tfy17pmk/dbt/GUI/assets/circle.png

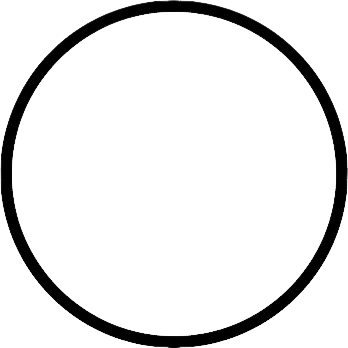
GUI/assets/circle.png
