tfy17pmk/dbt/GUI/assets/competition.png

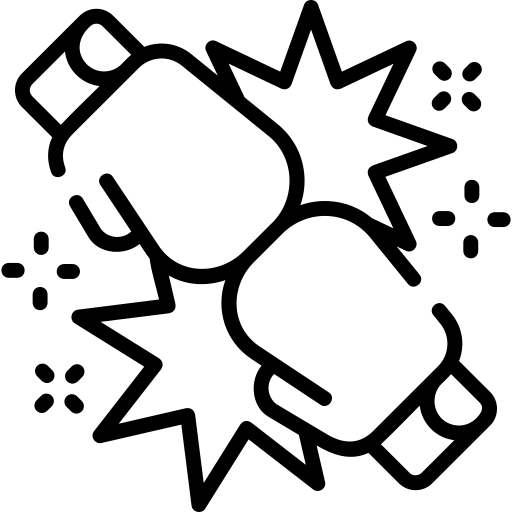
GUI/assets/competition.png
