tfy17pmk/dbt/GUI/assets/ENFlag.png

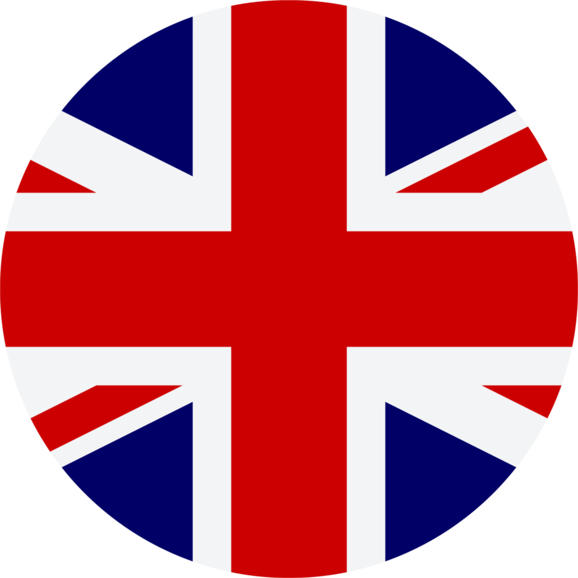
GUI/assets/ENFlag.png
