tfy17pmk/dbt/GUI/assets/heart.png

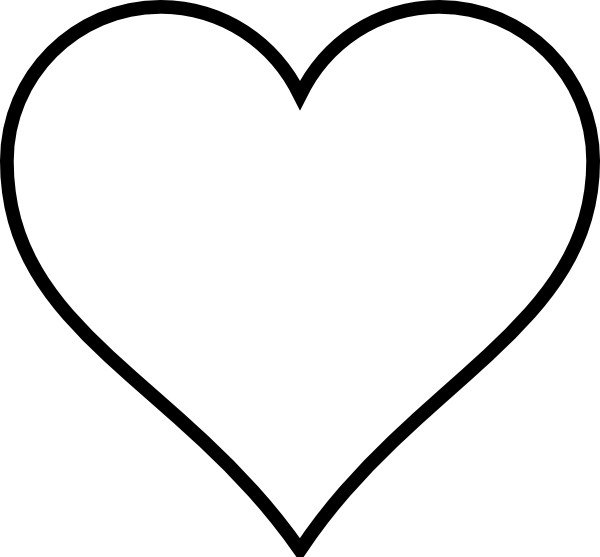
GUI/assets/heart.png
