tfy17pmk/dbt/Parts/waterLaserCutting/3mmMDF/BottomRoundBox.dxf

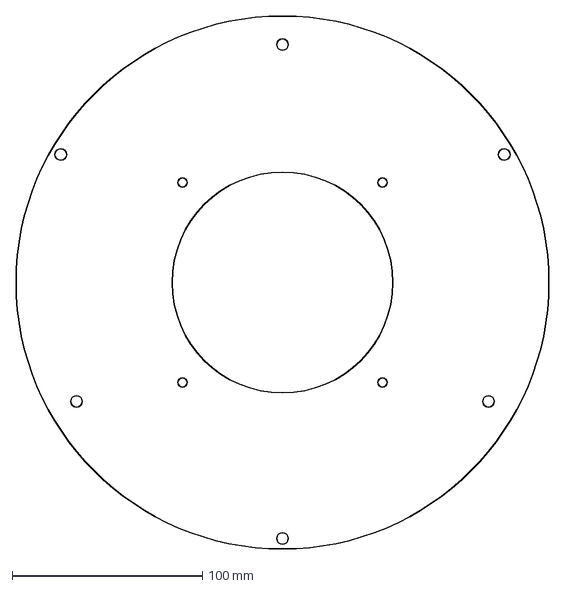
[picture p23: CAD file, 2024-12-10]
Parts/waterLaserCutting/3mmMDF/BottomRoundBox.dxf
280.0 x 280.0 mm
