tfy17pmk/dbt/Parts/waterLaserCutting/3mmMDF/CirkularBoxInsert/Bottom.dxf

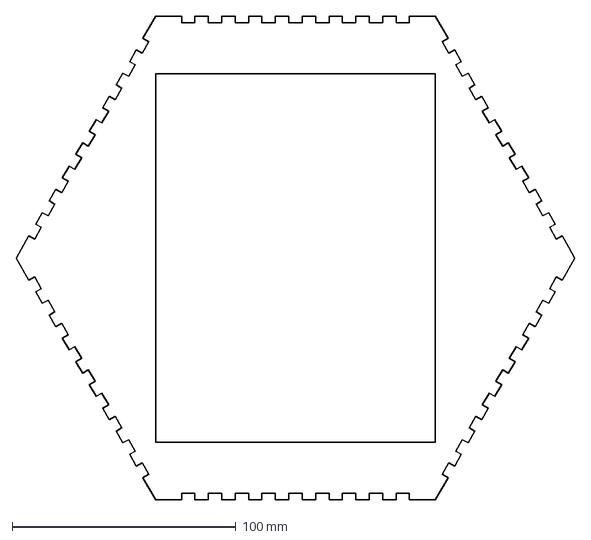
[picture p24: CAD file, 2024-12-10]
Parts/waterLaserCutting/3mmMDF/CirkularBoxInsert/Bottom.dxf
250.0 x 216.5 mm
