tfy17pmk/dbt/Parts/waterLaserCutting/metal/MonitorCover1mm.dxf

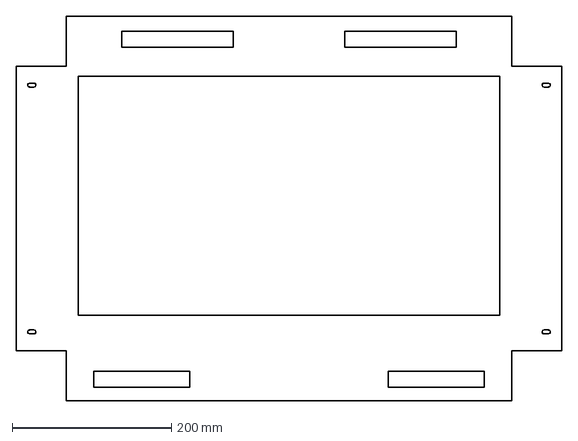
[picture p25: CAD file, 2024-12-17]
Parts/waterLaserCutting/metal/MonitorCover1mm.dxf
685.3 x 483.3 mm
