tfy17pmk/dbt/Parts/stl Files/Arm/LowerArmpartB.stl

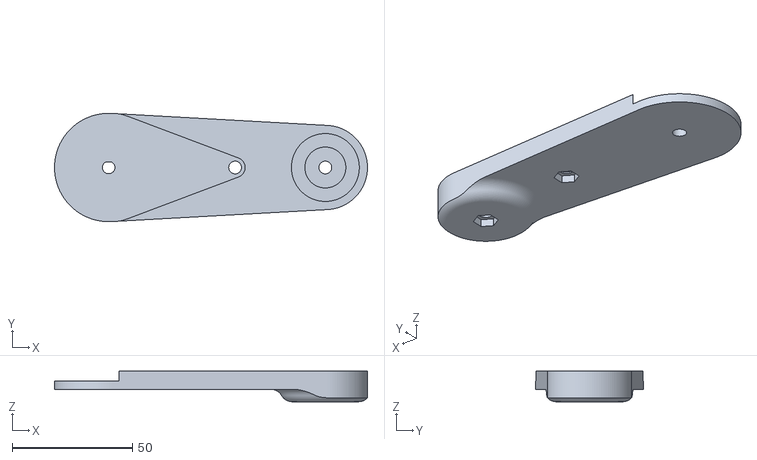
[picture p26: CAD file, 2024-12-10]
Parts/stl Files/Arm/LowerArmpartB.stl
130.0 x 45.0 x 12.7
