tfy17pmk/dbt/Parts/stl Files/Balance Plate Mounting Bracket/BottomBracket.stl

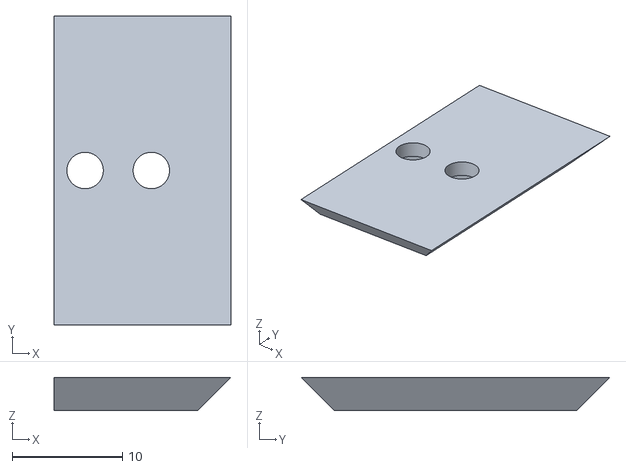
[picture p27: CAD file, 2024-12-10]
Parts/stl Files/Balance Plate Mounting Bracket/BottomBracket.stl
16.0 x 28.0 x 3.00
