tfy17pmk/dbt/Parts/stl Files/PSUcover.stl

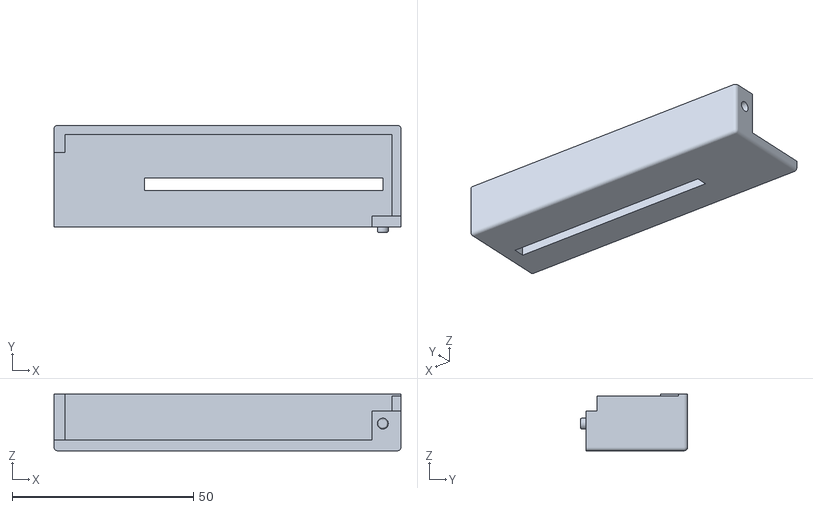
[picture p28: CAD file, 2024-12-10]
Parts/stl Files/PSUcover.stl
95.6 x 29.6 x 15.6
