tfy17pmk/dbt/Parts/waterLaserCutting/metal/SmalMetalRingWithNotch3mm.dxf

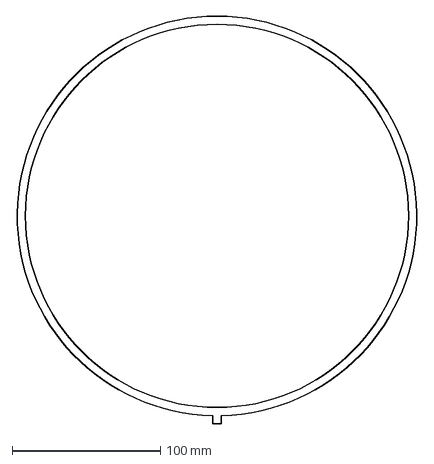
[picture p29: CAD file, 2024-12-10]
Parts/waterLaserCutting/metal/SmalMetalRingWithNotch3mm.dxf
270.6 x 274.5 mm
