tfy17pmk/dbt/Parts/stl Files/CableClip.stl

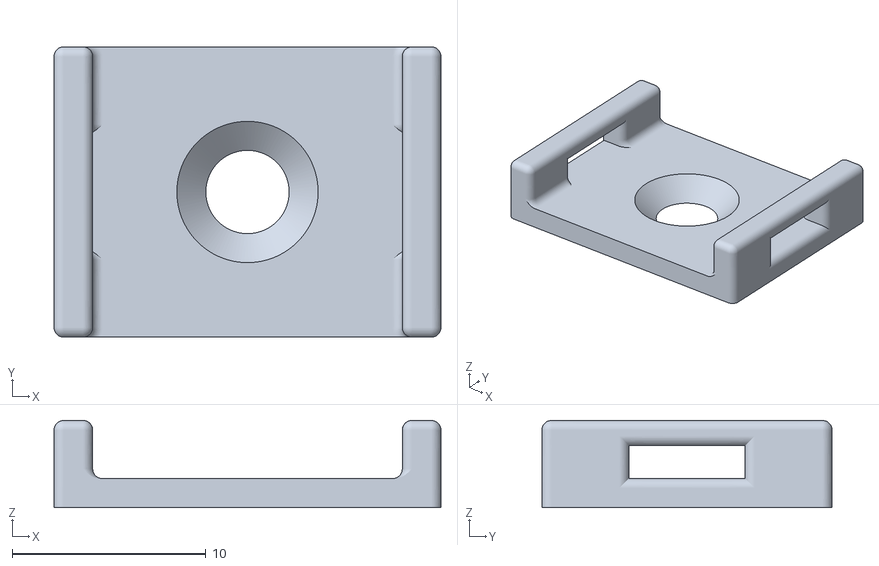
[picture p30: CAD file, 2024-12-10]
Parts/stl Files/CableClip.stl
20.0 x 15.0 x 4.50
