tfy17pmk/dbt/Parts/waterLaserCutting/metal/BaseplateWithSmalerHoles3mm.dxf

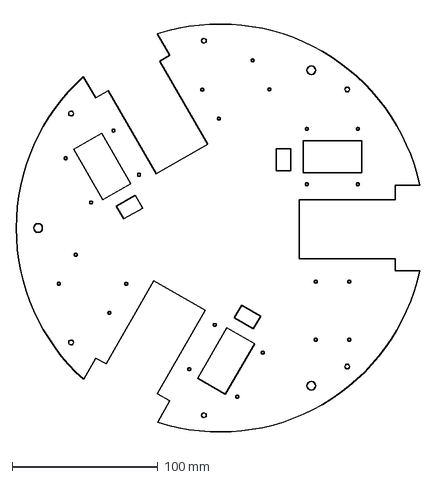
[picture p31: CAD file, 2024-12-10]
Parts/waterLaserCutting/metal/BaseplateWithSmalerHoles3mm.dxf
276.9 x 290.8 mm
