tfy17pmk/dbt/Parts/waterLaserCutting/metal/FeetPlate3mm.dxf

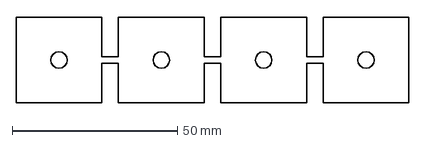
[picture p32: CAD file, 2024-12-10]
Parts/waterLaserCutting/metal/FeetPlate3mm.dxf
119.0 x 26.0 mm
