tfy17pmk/dbt/Parts/waterLaserCutting/metal/LargeMetalRingWithMountingFlange3mm.dxf

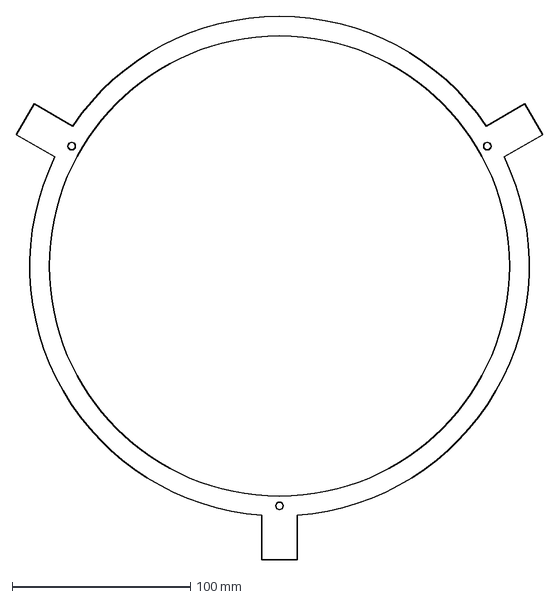
[picture p33: CAD file, 2024-12-10]
Parts/waterLaserCutting/metal/LargeMetalRingWithMountingFlange3mm.dxf
295.2 x 304.6 mm
