tfy17pmk/dbt/Parts/waterLaserCutting/metal/ArmReinforsment3mm.dxf

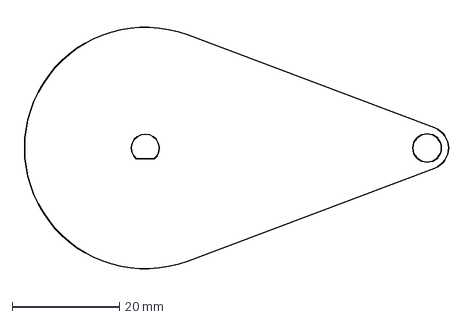
[picture p34: CAD file, 2024-12-10]
Parts/waterLaserCutting/metal/ArmReinforsment3mm.dxf
80.5 x 49.2 mm
