tfy17pmk/dbt/Parts/waterLaserCutting/metal/MonitorMountPlate1mm.dxf

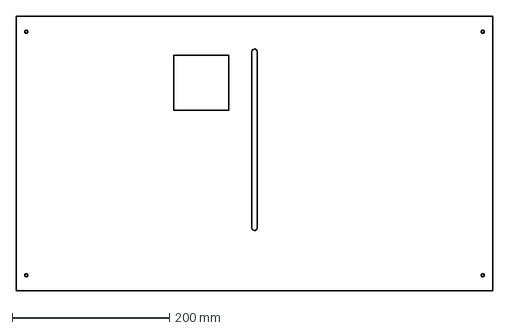
[picture p35: CAD file, 2024-12-10]
Parts/waterLaserCutting/metal/MonitorMountPlate1mm.dxf
606.3 x 350.0 mm
